The0Scorpion/2DOF_Hover/CAD/Inertias/InertiaHigherJoint.PNG

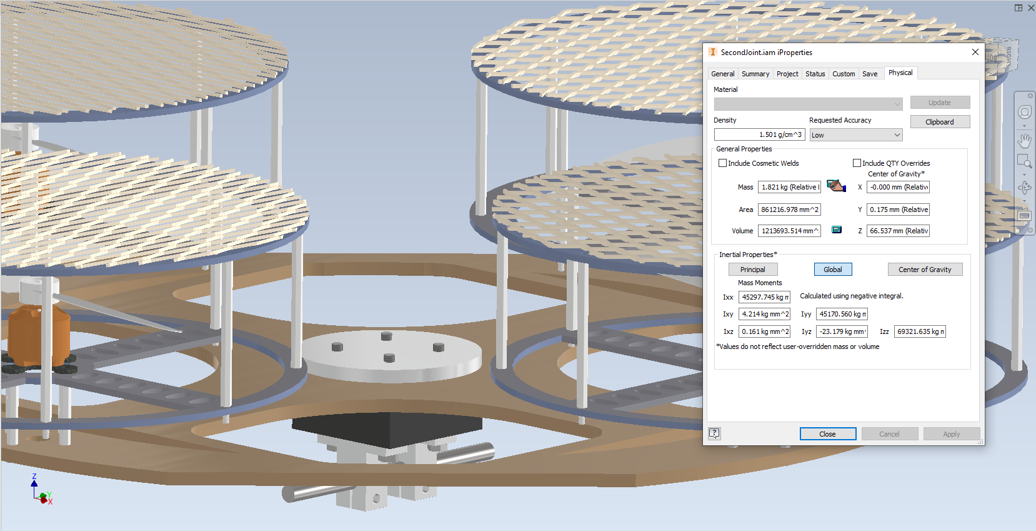
CAD/Inertias/InertiaHigherJoint.PNG
