The0Scorpion/2DOF_Hover/CAD/Inertias/LowerJoint_CG.PNG

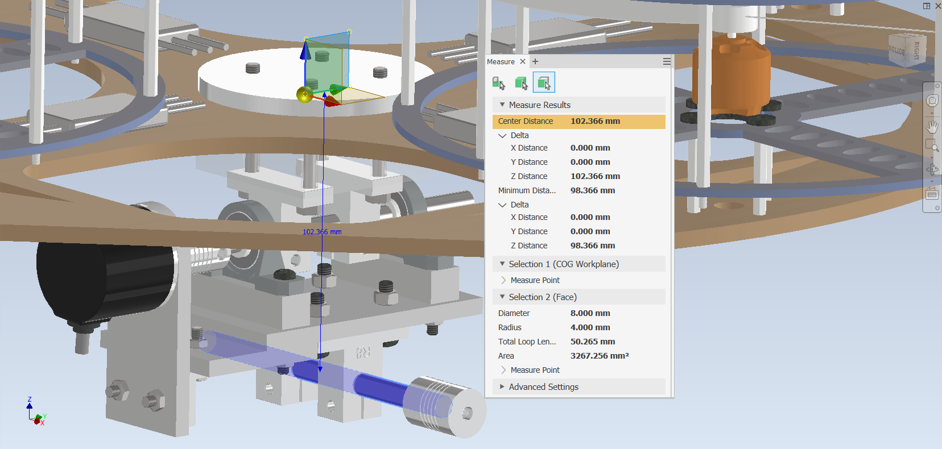
CAD/Inertias/LowerJoint_CG.PNG
