The0Scorpion/2DOF_Hover/CAD/Inertias/LowerJoint_Inertia_mass.PNG

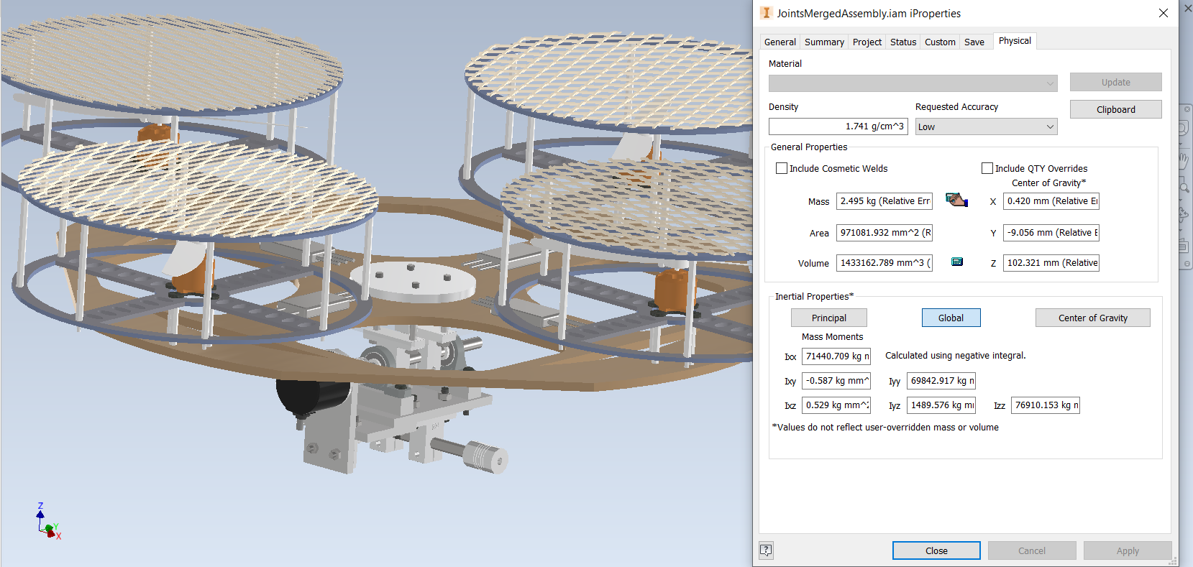
CAD/Inertias/LowerJoint_Inertia_mass.PNG
