The0Scorpion/2DOF_Hover/CAD/Inertias/LowerJoint_TorqueArm.PNG

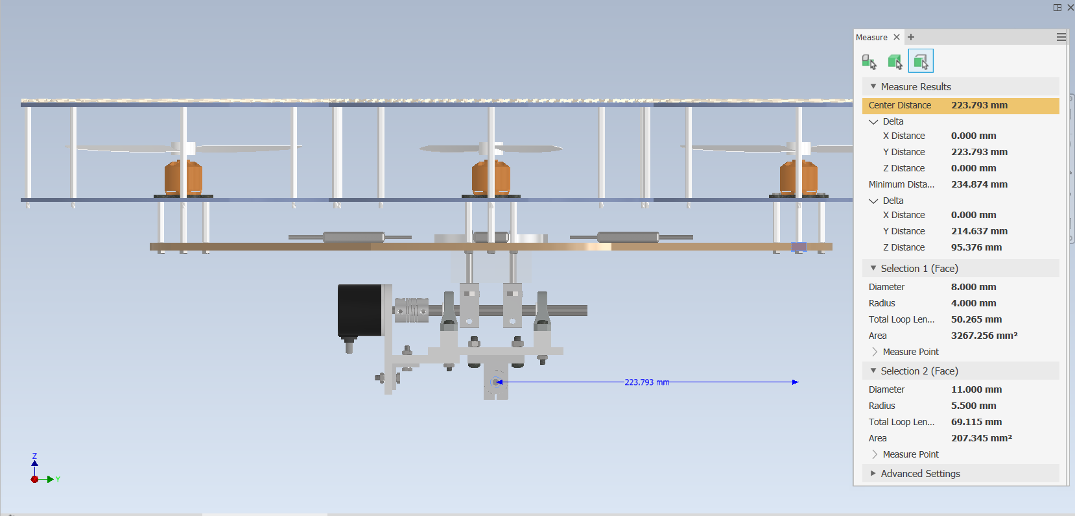
CAD/Inertias/LowerJoint_TorqueArm.PNG
