The0Scorpion/2DOF_Hover/CAD/Inertias/UpperJoint_CG.PNG

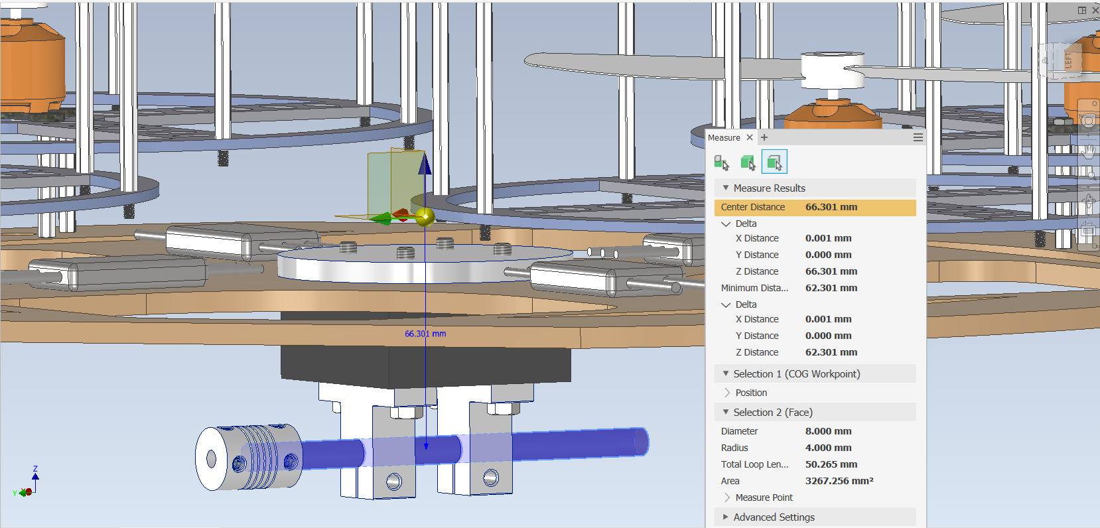
CAD/Inertias/UpperJoint_CG.PNG
