The0Scorpion/2DOF_Hover/CAD/Inertias/UpperJoint_TorqueArm.PNG

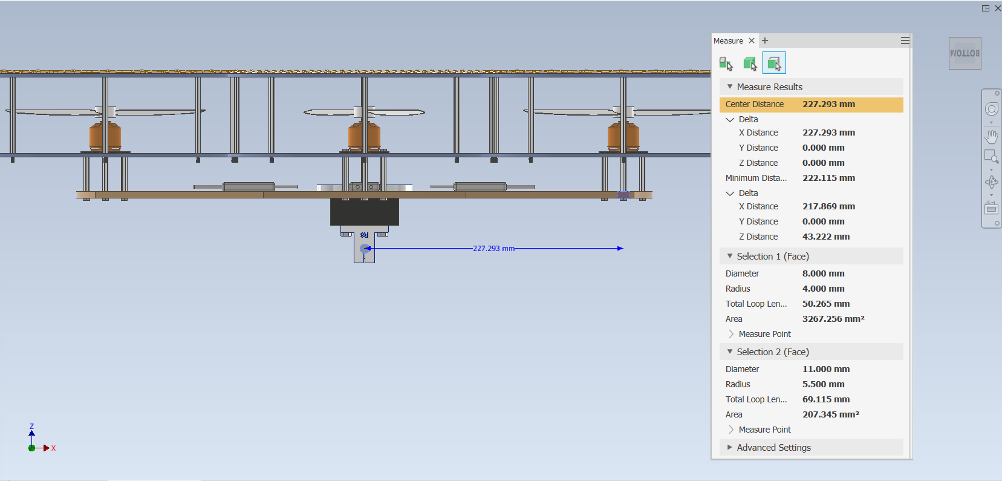
CAD/Inertias/UpperJoint_TorqueArm.PNG
