The0Scorpion/2DOF_Hover/Electric/PCB_HighQuality_2024-03-02.png

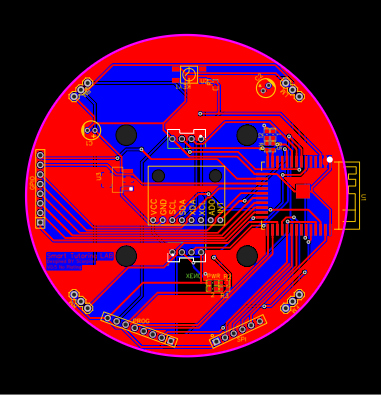
Electric/PCB_HighQuality_2024-03-02.png
