The0Scorpion/2DOF_Hover/Electric/Screenshot 2024-03-02 193824.png

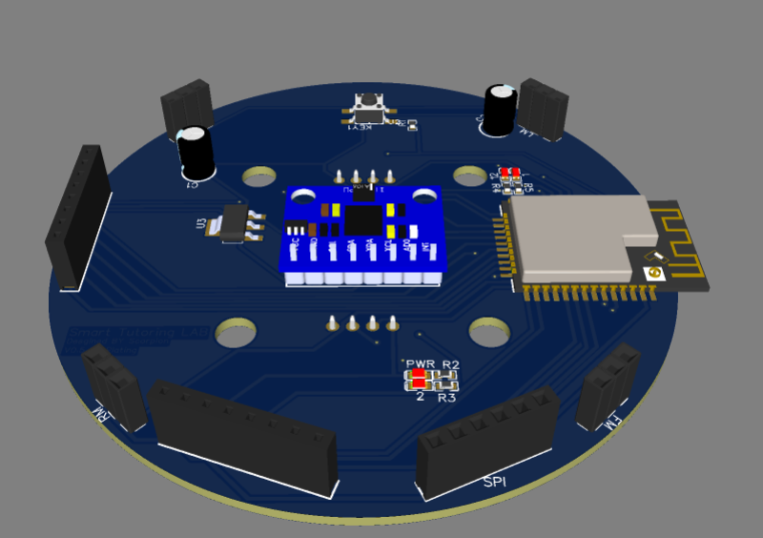
Electric/Screenshot 2024-03-02 193824.png
