The0Scorpion/2DOF_Hover/Model/MotorEstimationModel/Inertias/ArmLengthLower.PNG

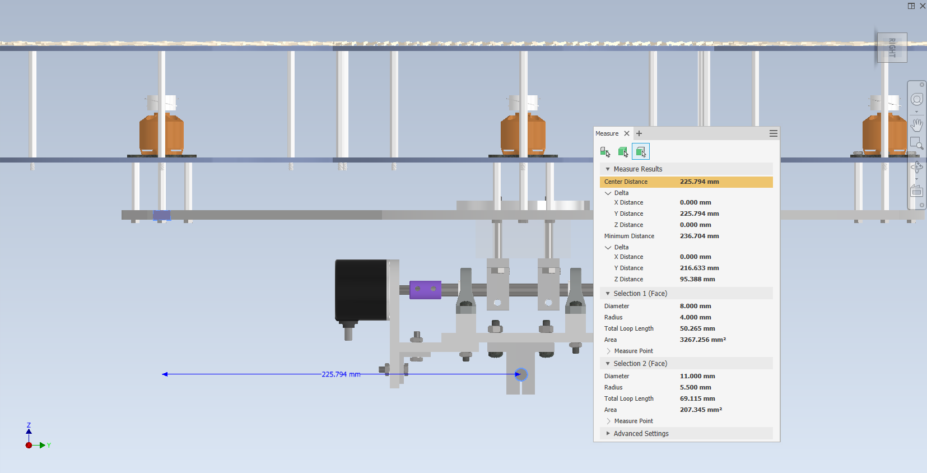
Model/MotorEstimationModel/Inertias/ArmLengthLower.PNG
