The0Scorpion/2DOF_Hover/Model/MotorEstimationModel/Inertias/ArmLengthUpper.PNG

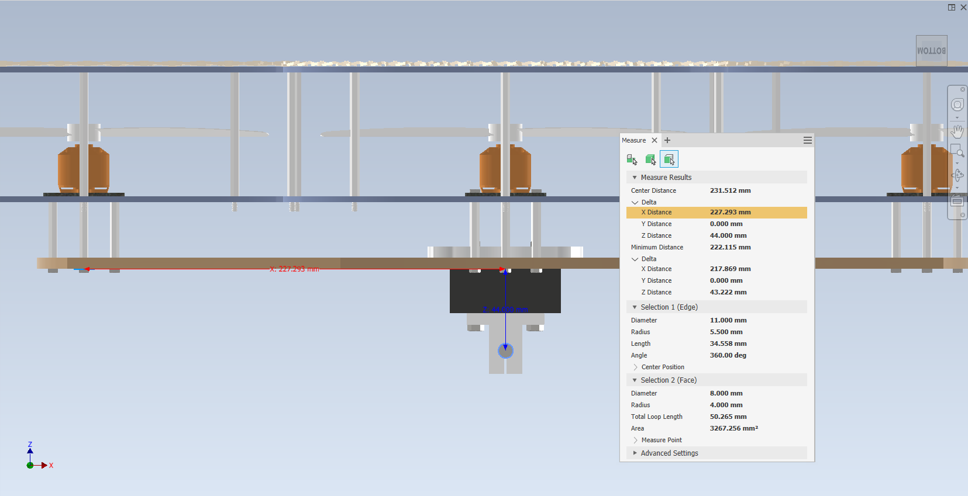
Model/MotorEstimationModel/Inertias/ArmLengthUpper.PNG
