The0Scorpion/2DOF_Hover/Model/MotorEstimationModel/Inertias/CG_LowerJoint.PNG

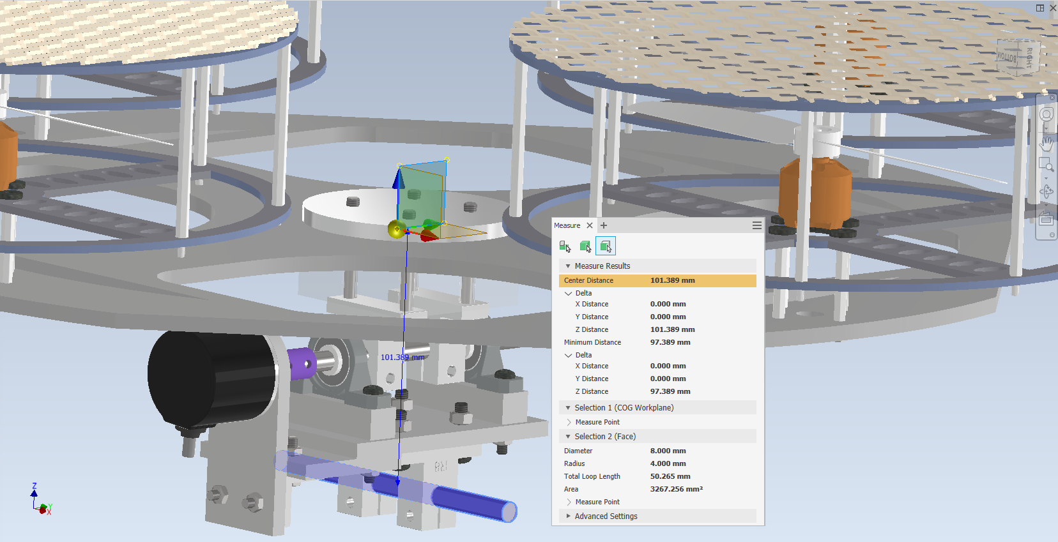
Model/MotorEstimationModel/Inertias/CG_LowerJoint.PNG
