The0Scorpion/2DOF_Hover/Model/MotorEstimationModel/Inertias/CG_UpperJoint.PNG

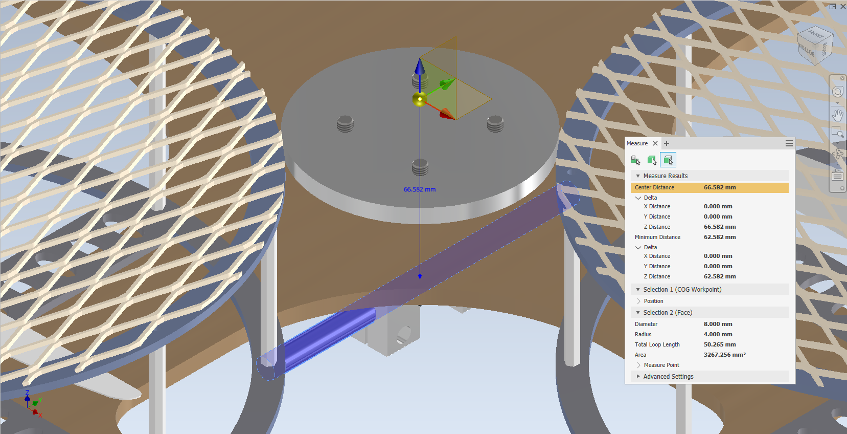
Model/MotorEstimationModel/Inertias/CG_UpperJoint.PNG
