The0Scorpion/2DOF_Hover/Model/MotorEstimationModel/Inertias/InertiaUpperJoint.PNG

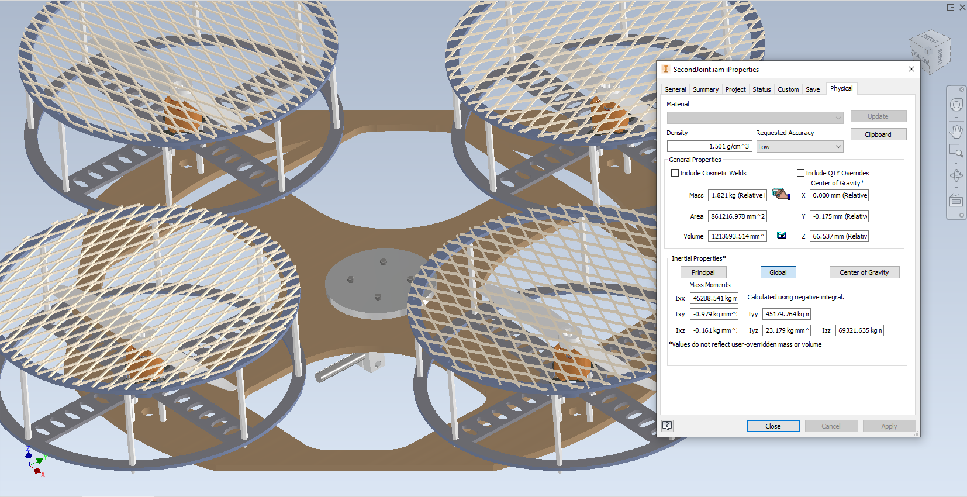
Model/MotorEstimationModel/Inertias/InertiaUpperJoint.PNG
