The0Scorpion/2DOF_Hover/Model/Roll Reduced Model/2200kv.jpg

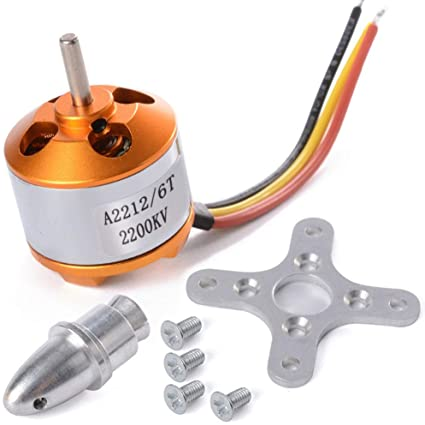
Model/Roll Reduced Model/2200kv.jpg
