The0Scorpion/2DOF_Hover/Model/Non Linear Model/2020RightAngle_ipt_a59fb1f2.STEP

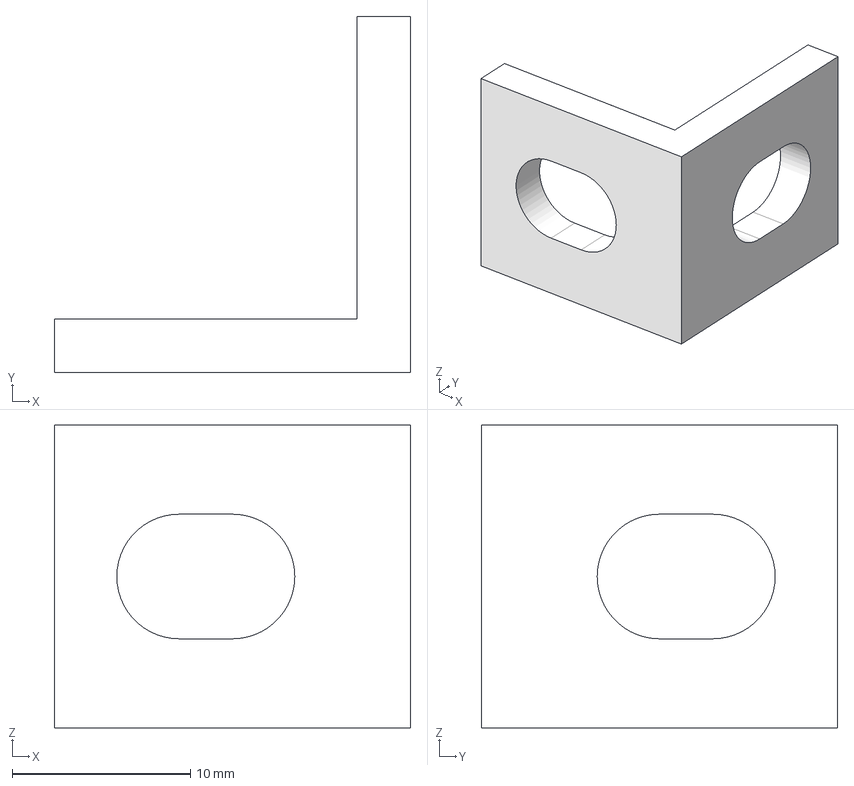
[picture p27: CAD file, 2024-03-01]
Model/Non Linear Model/2020RightAngle_ipt_a59fb1f2.STEP
20.0 x 20.0 x 17.0 mm
