The0Scorpion/2DOF_Hover/Model/Non Linear Model/BaseC_6_ipt_475c7a50.STEP

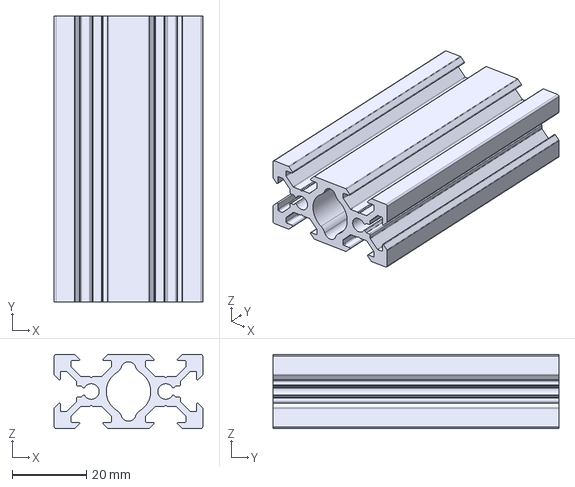
[picture p28: CAD file, 2024-03-01]
Model/Non Linear Model/BaseC_6_ipt_475c7a50.STEP
40.0 x 77.0 x 20.0 mm
