The0Scorpion/2DOF_Hover/Model/Non Linear Model/BaseC_3_ipt_c71fdd73.STEP

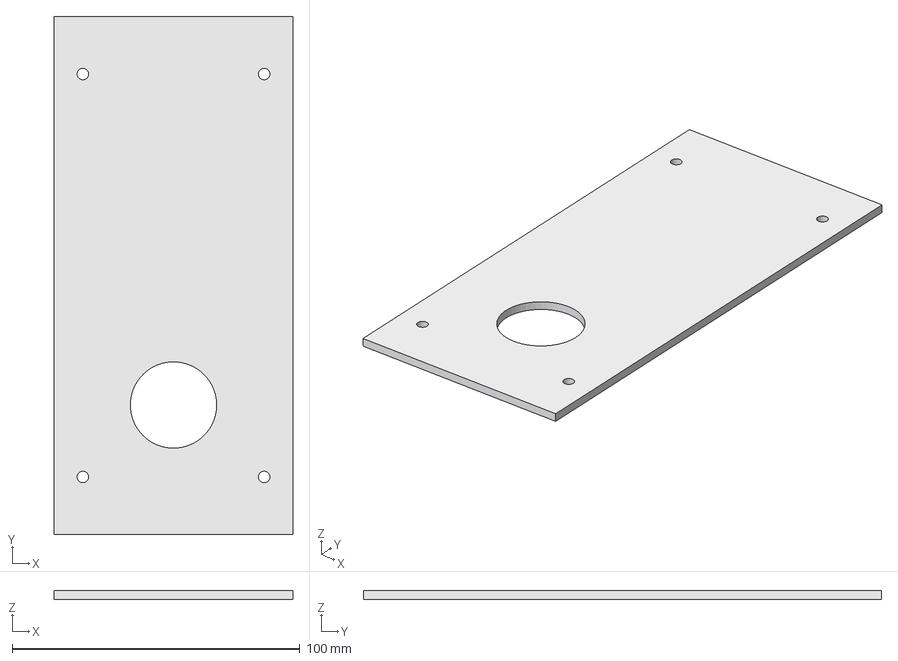
[picture p29: CAD file, 2024-03-01]
Model/Non Linear Model/BaseC_3_ipt_c71fdd73.STEP
83.0 x 180.0 x 3.00 mm
