The0Scorpion/2DOF_Hover/Model/Non Linear Model/spacers for prop_ipt_213f8d71.STEP

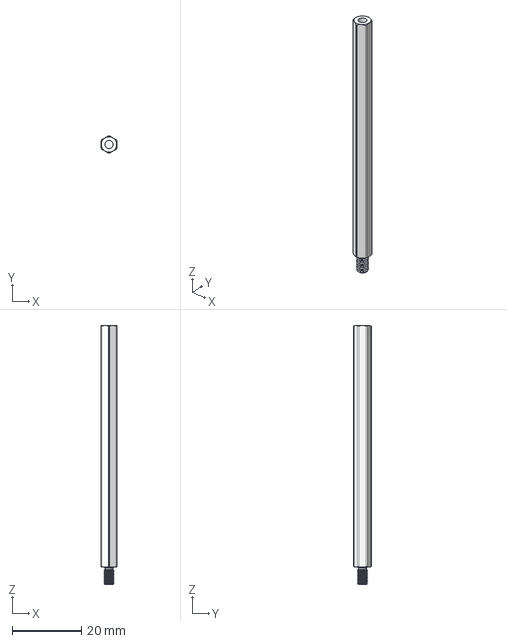
[picture p30: CAD file, 2024-03-01]
Model/Non Linear Model/spacers for prop_ipt_213f8d71.STEP
4.50 x 5.08 x 75.0 mm
