The0Scorpion/2DOF_Hover/Model/Non Linear Model/MOTOR COUPLER CONNECTOR (1)_ipt_c41452cb.STEP

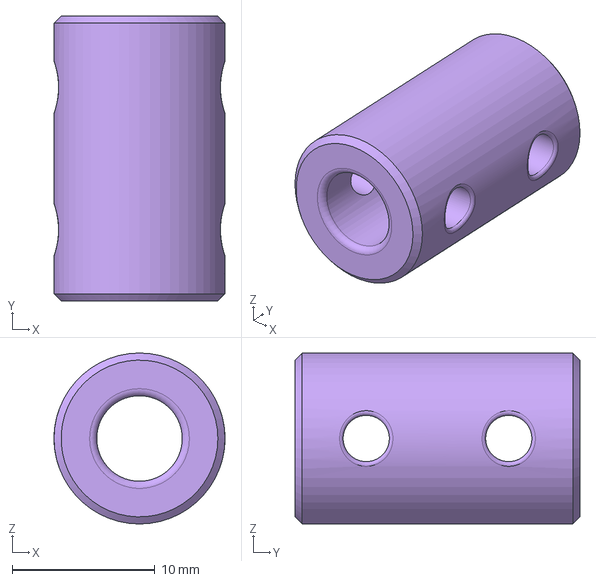
[picture p31: CAD file, 2024-03-01]
Model/Non Linear Model/MOTOR COUPLER CONNECTOR (1)_ipt_c41452cb.STEP
12.0 x 20.0 x 12.0 mm
