The0Scorpion/2DOF_Hover/Model/Non Linear Model/BaseC_4_ipt_c71fdd73.STEP

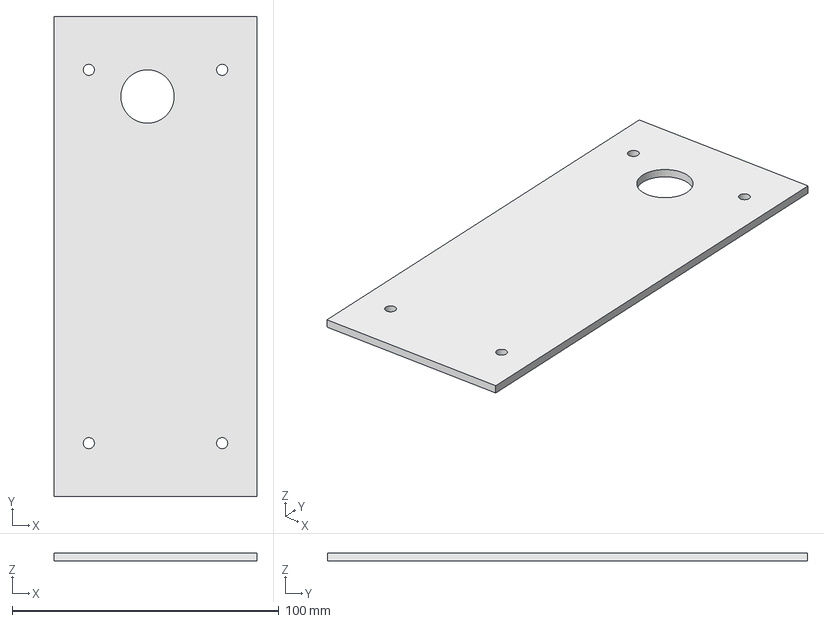
[picture p32: CAD file, 2024-03-01]
Model/Non Linear Model/BaseC_4_ipt_c71fdd73.STEP
76.0 x 180.0 x 3.00 mm
