The0Scorpion/2DOF_Hover/Model/Non Linear Model/Part1_ipt_db55b04b.STEP

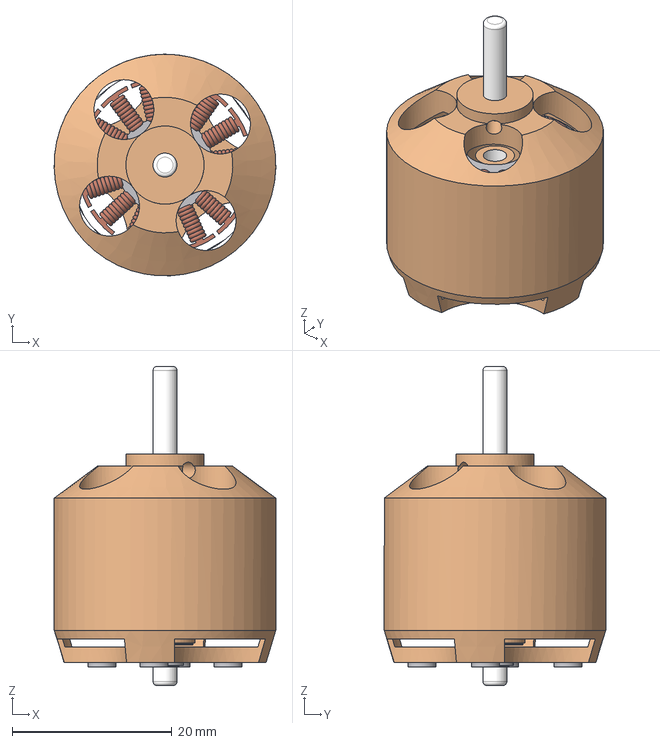
[picture p33: CAD file, 2024-03-01]
Model/Non Linear Model/Part1_ipt_db55b04b.STEP
27.8 x 27.8 x 40.0 mm
