The0Scorpion/2DOF_Hover/Model/Non Linear Model/Holder Tube-R8_ipt_e7239e0e.STEP

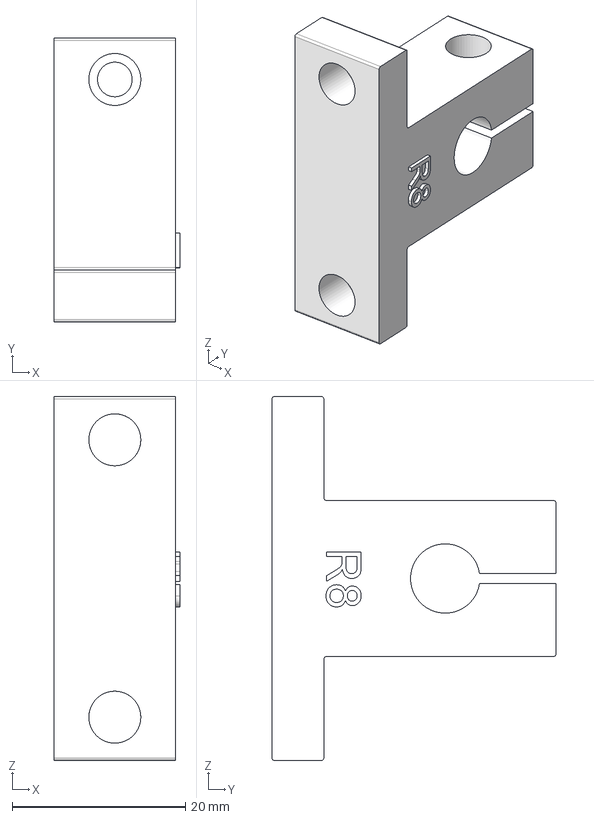
[picture p34: CAD file, 2024-03-01]
Model/Non Linear Model/Holder Tube-R8_ipt_e7239e0e.STEP
14.5 x 32.8 x 42.0 mm
