The0Scorpion/2DOF_Hover/Model/Non Linear Model/FlangedBearing8mm_ipt_45b851ef.STEP

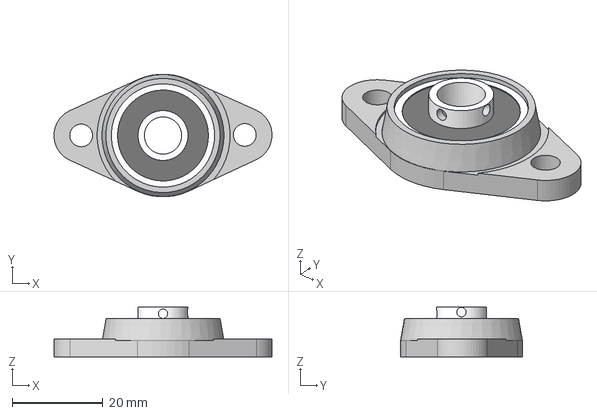
[picture p35: CAD file, 2024-03-01]
Model/Non Linear Model/FlangedBearing8mm_ipt_45b851ef.STEP
48.0 x 27.0 x 11.0 mm
