The0Scorpion/2DOF_Hover/Model/Non Linear Model/guard 2_ipt_d986c415.STEP

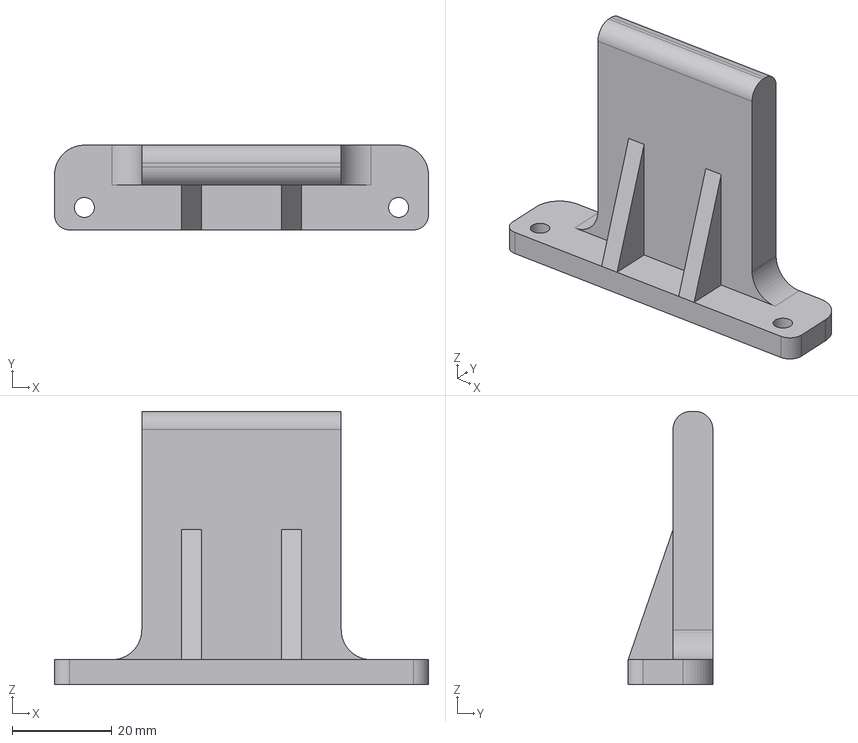
[picture p36: CAD file, 2024-03-01]
Model/Non Linear Model/guard 2_ipt_d986c415.STEP
75.0 x 17.0 x 54.8 mm
