The0Scorpion/2DOF_Hover/Model/Non Linear Model/pcb_ipt_b7a0ce45.STEP

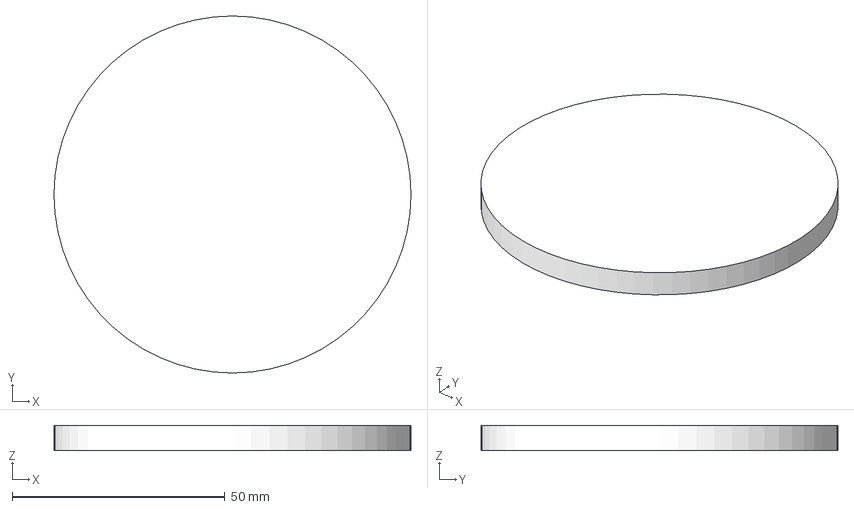
[picture p37: CAD file, 2024-03-01]
Model/Non Linear Model/pcb_ipt_b7a0ce45.STEP
84.0 x 84.0 x 6.00 mm
