The0Scorpion/2DOF_Hover/Model/Non Linear Model/gard1_ipt_e571afd1.STEP

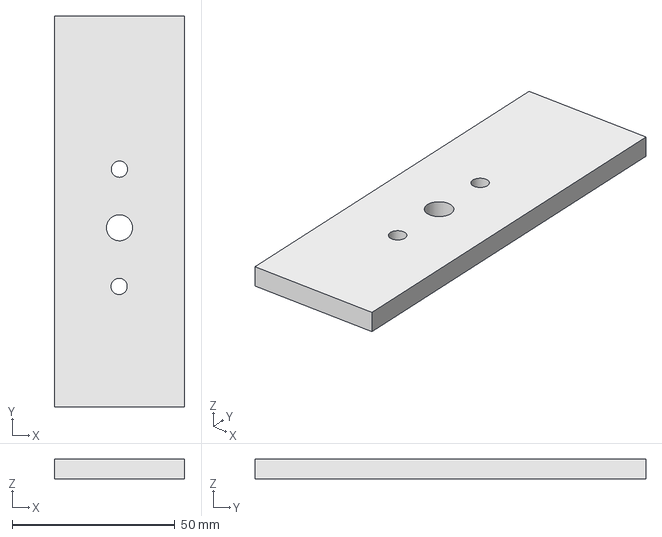
[picture p38: CAD file, 2024-03-01]
Model/Non Linear Model/gard1_ipt_e571afd1.STEP
40.0 x 120.0 x 6.00 mm
