The0Scorpion/2DOF_Hover/Model/Non Linear Model/Joint1C_1_ipt_b9e6bb9f.STEP

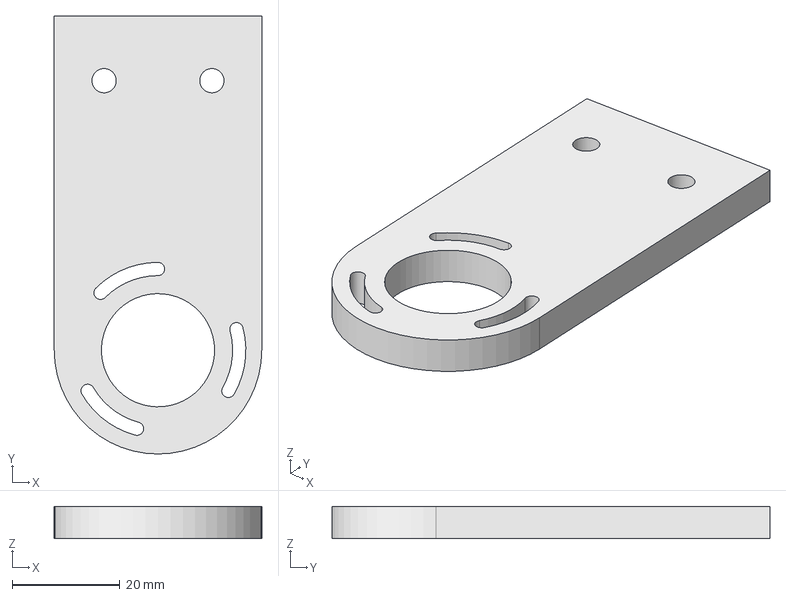
[picture p39: CAD file, 2024-03-01]
Model/Non Linear Model/Joint1C_1_ipt_b9e6bb9f.STEP
38.5 x 81.2 x 6.00 mm
