The0Scorpion/2DOF_Hover/Model/Non Linear Model/interplate_ipt_43879ff1.STEP

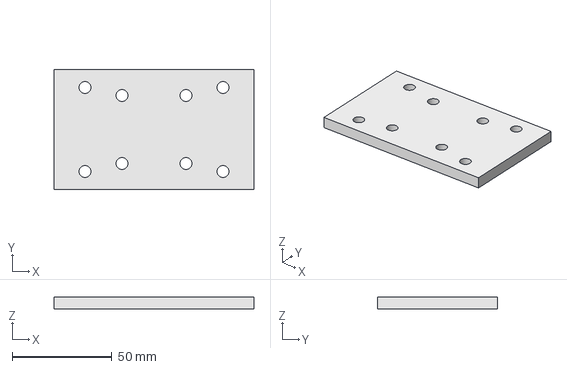
[picture p40: CAD file, 2024-03-01]
Model/Non Linear Model/interplate_ipt_43879ff1.STEP
100.0 x 60.0 x 6.00 mm
