The0Scorpion/2DOF_Hover/Model/Non Linear Model/Part18_ipt_c51c05df.STEP

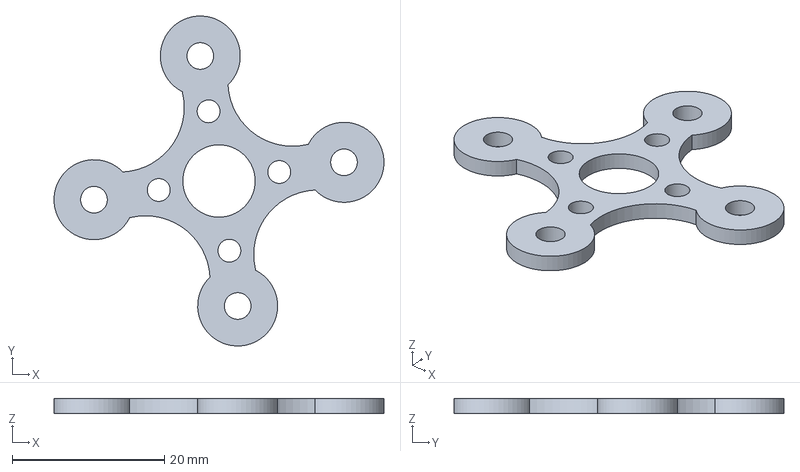
[picture p41: CAD file, 2024-03-01]
Model/Non Linear Model/Part18_ipt_c51c05df.STEP
43.3 x 43.3 x 2.00 mm
