The0Scorpion/2DOF_Hover/Model/Non Linear Model/Standoff M3 M-M H 45mm_ipt_213f8d71.STEP

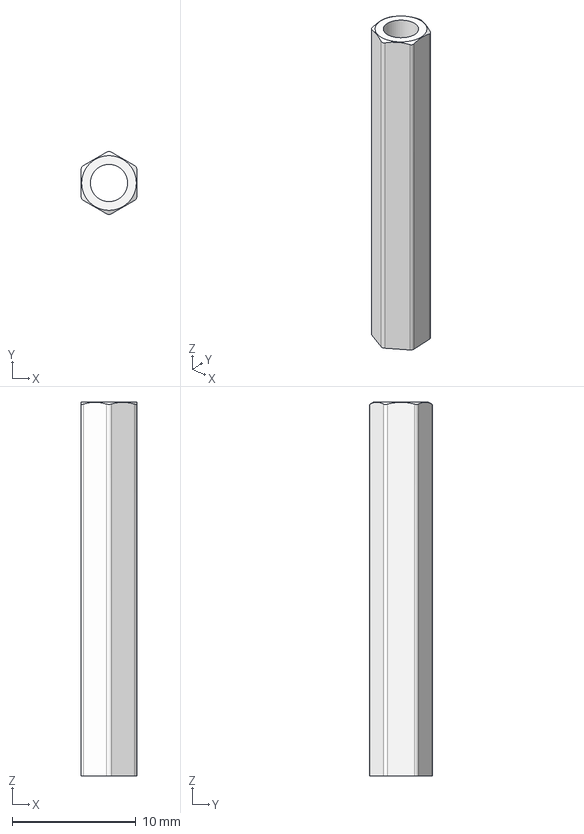
[picture p42: CAD file, 2024-03-01]
Model/Non Linear Model/Standoff M3 M-M H 45mm_ipt_213f8d71.STEP
4.50 x 5.08 x 30.2 mm
