The0Scorpion/2DOF_Hover/Model/Non Linear Model/Part15_ipt_e31f6ad0.STEP

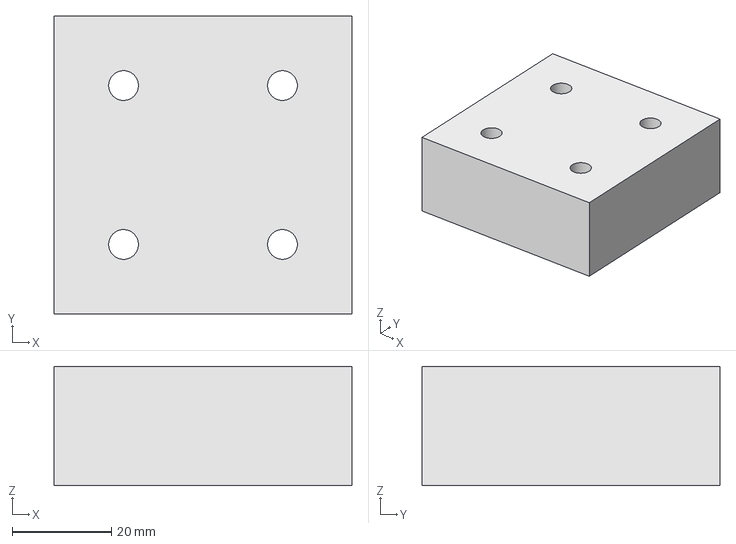
[picture p43: CAD file, 2024-03-01]
Model/Non Linear Model/Part15_ipt_e31f6ad0.STEP
60.0 x 60.0 x 24.0 mm
