The0Scorpion/2DOF_Hover/Model/Non Linear Model/Part17_ipt_34ea8653.STEP

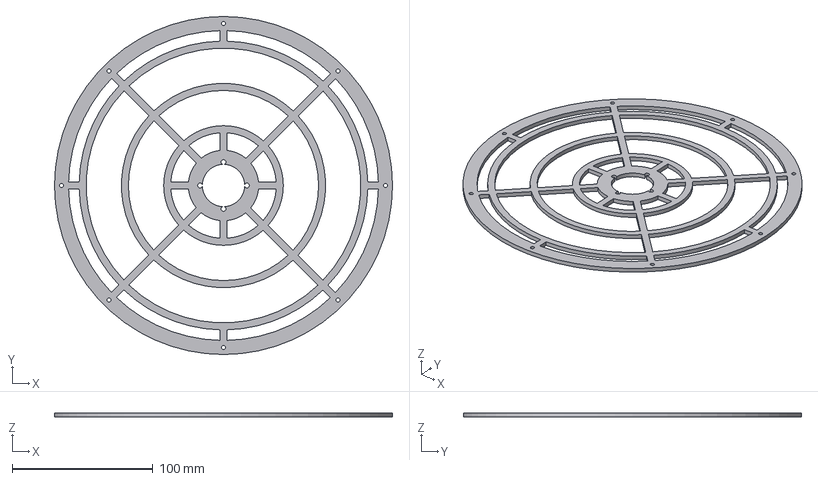
[picture p44: CAD file, 2024-03-01]
Model/Non Linear Model/Part17_ipt_34ea8653.STEP
240.0 x 240.0 x 3.00 mm
