The0Scorpion/2DOF_Hover/Model/Non Linear Model/plummer blockPowe_ipt_5ba01ddb.STEP

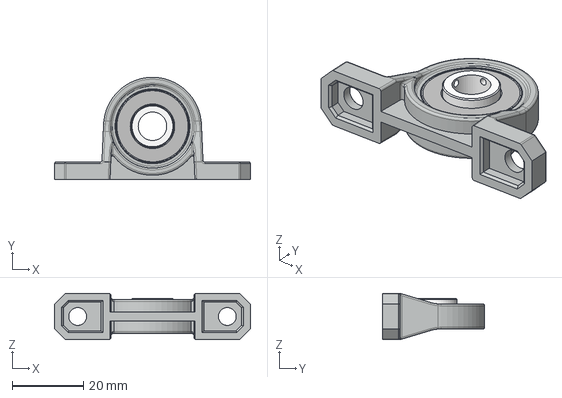
[picture p45: CAD file, 2024-03-01]
Model/Non Linear Model/plummer blockPowe_ipt_5ba01ddb.STEP
55.0 x 28.8 x 13.0 mm
