The0Scorpion/2DOF_Hover/Model/Non Linear Model/9. Fan_ipt_4f385e48.STEP

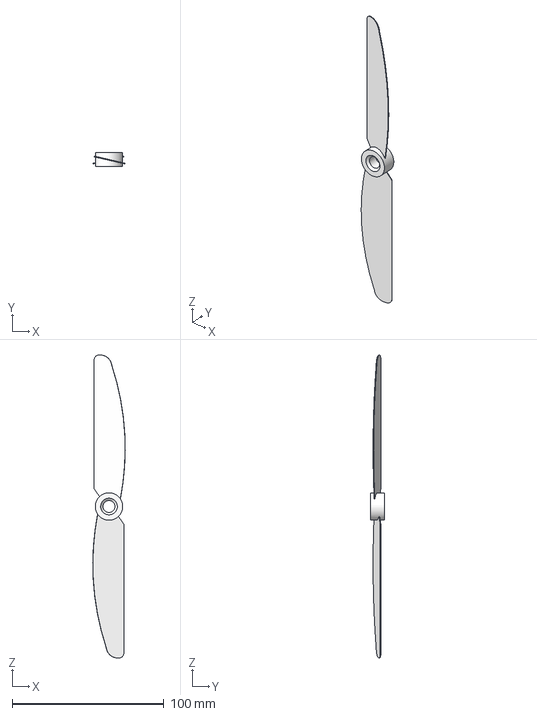
[picture p46: CAD file, 2024-03-01]
Model/Non Linear Model/9. Fan_ipt_4f385e48.STEP
21.4 x 9.42 x 199.4 mm
