The0Scorpion/2DOF_Hover/Model/Non Linear Model/BaseC_7_ipt_b9e6bb9f.STEP

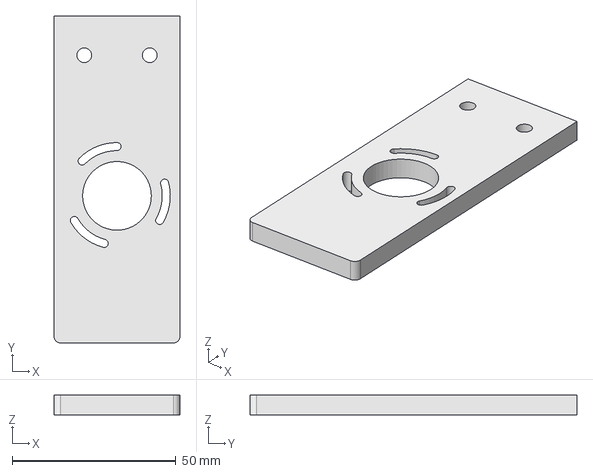
[picture p47: CAD file, 2024-03-01]
Model/Non Linear Model/BaseC_7_ipt_b9e6bb9f.STEP
38.5 x 100.0 x 6.00 mm
