The0Scorpion/2DOF_Hover/Model/Non Linear Model/BaseC_1_ipt_dbc63049.STEP

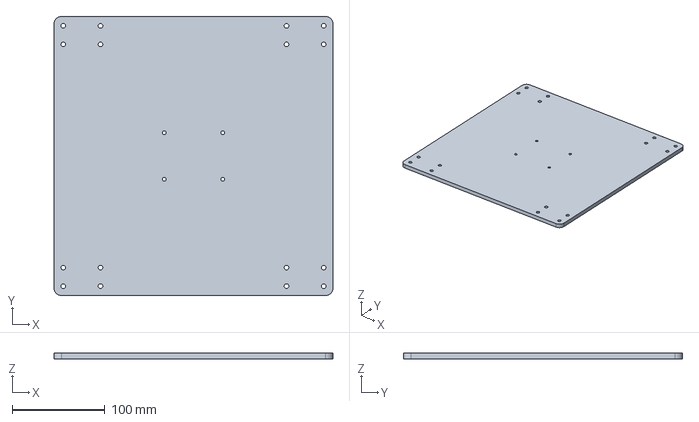
[picture p48: CAD file, 2024-03-01]
Model/Non Linear Model/BaseC_1_ipt_dbc63049.STEP
300.0 x 300.0 x 6.00 mm
