The0Scorpion/2DOF_Hover/Model/Non Linear Model/plateplummer_ipt_bf847d22.STEP

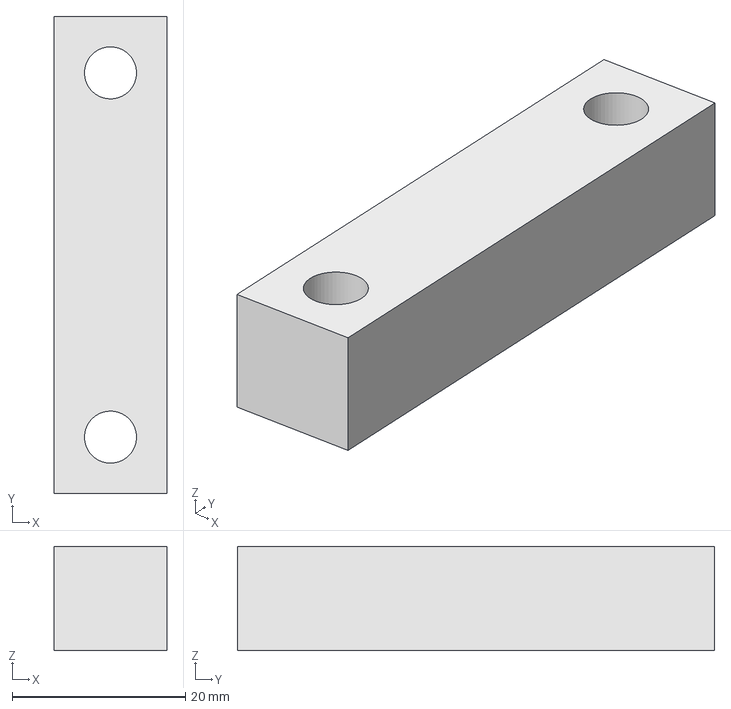
[picture p49: CAD file, 2024-03-01]
Model/Non Linear Model/plateplummer_ipt_bf847d22.STEP
13.0 x 55.0 x 12.0 mm
