The0Scorpion/2DOF_Hover/Model/Non Linear Model/BaseC_9_ipt_bd9223d9.STEP

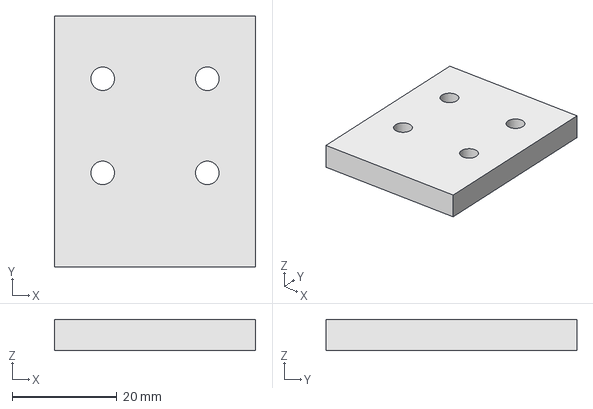
[picture p50: CAD file, 2024-03-01]
Model/Non Linear Model/BaseC_9_ipt_bd9223d9.STEP
38.5 x 48.0 x 6.00 mm
