The0Scorpion/2DOF_Hover/Model/Non Linear Model/20x20mm V-Slot_ipt_b09f816c.STEP

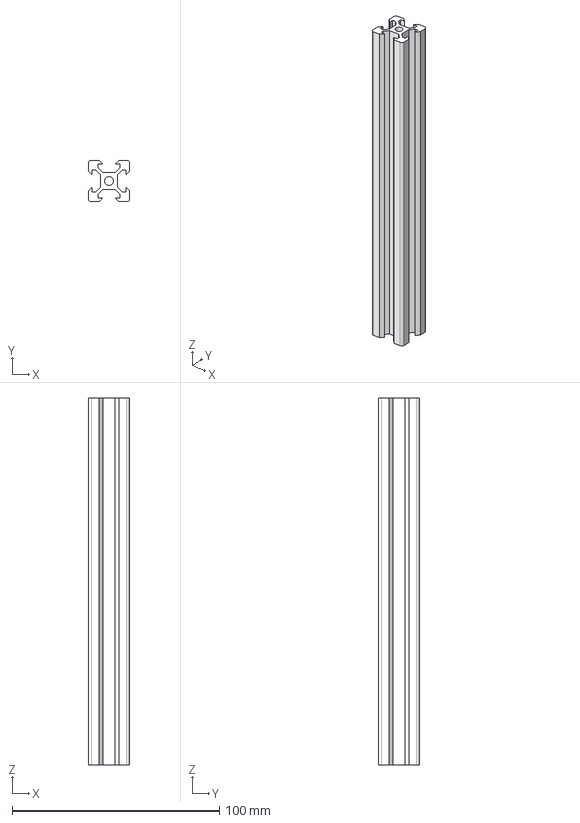
[picture p51: CAD file, 2024-03-01]
Model/Non Linear Model/20x20mm V-Slot_ipt_b09f816c.STEP
20.0 x 20.0 x 177.0 mm
