The0Scorpion/2DOF_Hover/Model/Non Linear Model/plateencoder_ipt_139437e7.STEP

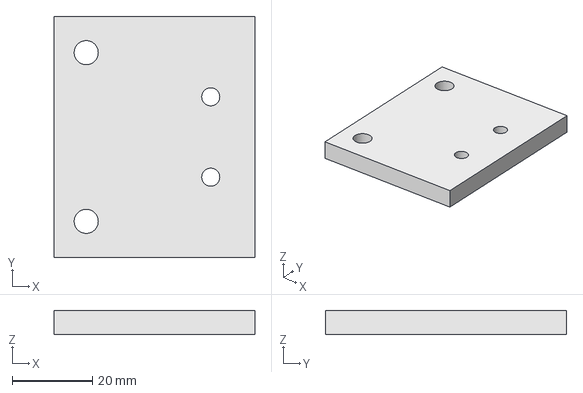
[picture p52: CAD file, 2024-03-01]
Model/Non Linear Model/plateencoder_ipt_139437e7.STEP
50.0 x 60.0 x 6.00 mm
