The0Scorpion/2DOF_Hover/Model/Non Linear Model/guard3_ipt_8caca9e3.STEP

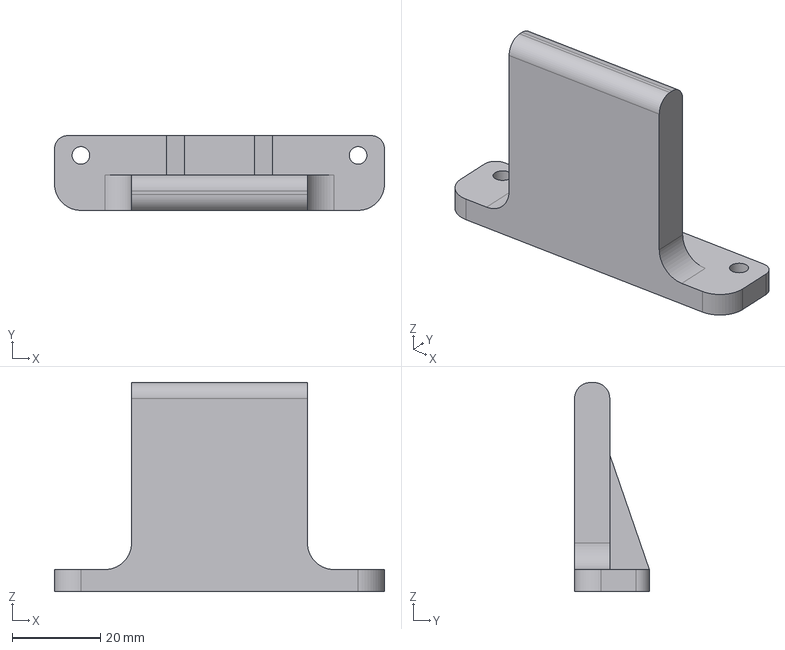
[picture p53: CAD file, 2024-03-01]
Model/Non Linear Model/guard3_ipt_8caca9e3.STEP
75.0 x 17.0 x 47.5 mm
