The0Scorpion/2DOF_Hover/Model/Non Linear Model/Part16_ipt_fb07ed32.STEP

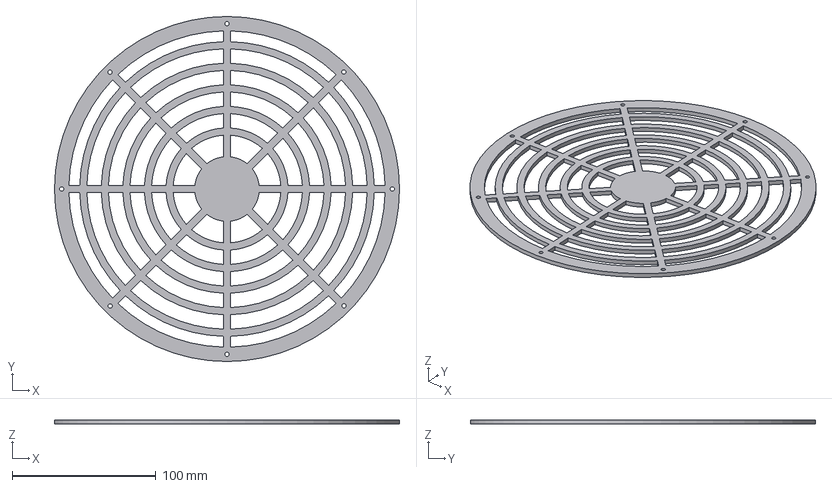
[picture p54: CAD file, 2024-03-01]
Model/Non Linear Model/Part16_ipt_fb07ed32.STEP
240.0 x 240.0 x 3.00 mm
