The0Scorpion/2DOF_Hover/Model/Non Linear Model/BaseC_5_ipt_c71fdd73.STEP

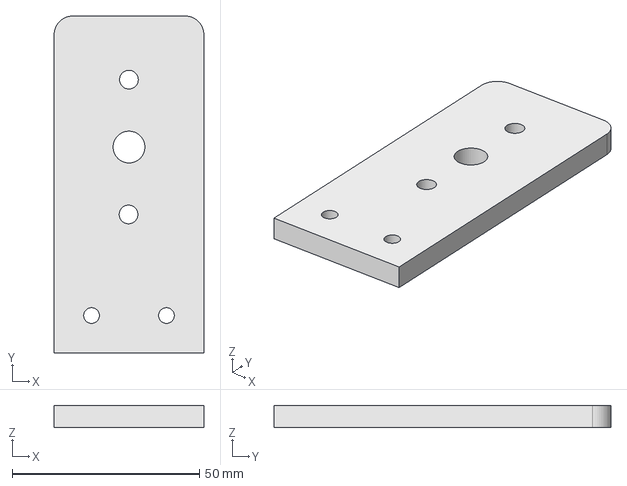
[picture p55: CAD file, 2024-03-01]
Model/Non Linear Model/BaseC_5_ipt_c71fdd73.STEP
40.0 x 90.0 x 6.00 mm
