The0Scorpion/2DOF_Hover/Data/MQTT_Delay_Test2024-03-17 18-24.xlsx

Pkt ID | pkt Size | Send Time | Receive Time | pkt Delay(ms) | Time from last pkt
1 | 121 | 1710692800280 | 1710692800314 | 34 | 500
2 | 121 | 1710692800780 | 1710692800818 | 38 | 504
3 | 121 | 1710692801280 | 1710692801315 | 35 | 497
4 | 121 | 1710692801780 | 1710692801827 | 47 | 512
5 | 121 | 1710692802280 | 1710692802318 | 38 | 491 | Test Conditions:
6 | 121 | 1710692802780 | 1710692802840 | 60 | 522 | NTP Server: | time.aws.com
7 | 121 | 1710692803280 | 1710692803315 | 35 | 475 | pkt Size | 121
8 | 121 | 1710692803780 | 1710692803815 | 35 | 500 | RTT to AWS | 44ms | (measured on same network)
9 | 121 | 1710692804280 | 1710692804316 | 36 | 501 | RTT to AWS NTP | 280ms | (measured on same network)
10 | 122 | 1710692804780 | 1710692804814 | 34 | 498 | RTT to google dns | 44ms | (measured on same network)
11 | 122 | 1710692805280 | 1710692805325 | 45 | 511
12 | 122 | 1710692805780 | 1710692805822 | 42 | 497
13 | 122 | 1710692806280 | 1710692806319 | 39 | 497
14 | 122 | 1710692806780 | 1710692806816 | 36 | 497
15 | 122 | 1710692807280 | 1710692807317 | 37 | 501
16 | 122 | 1710692807780 | 1710692807816 | 36 | 499
17 | 122 | 1710692808280 | 1710692808314 | 34 | 498
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
