The0Scorpion/2DOF_Hover/Data/MQTT_Delay_Test2024-03-17 19-03.xlsx

Pkt ID | pkt Size | Send Time | Receive Time | pkt Delay(ms) (ESP TIME TO AWS) | Time from last pkt(Esp Time) | Local Time | LocalEpoch | Delay(Local Time to NodeJS Client) | Time from last pkt (in local Time)
1 | 121 | 1710695014510 | 1710695014539 | 29 | 500 | 19:03:34.514 | 68614514 | 25.00 | 500
2 | 121 | 1710695015010 | 1710695015042 | 32 | 503 | 19:03:34.985 | 68614985 | 57.00 | 471
3 | 121 | 1710695015510 | 1710695015541 | 31 | 499 | 19:03:35.502 | 68615502 | 39.00 | 517 | Test Conditions:
4 | 121 | 1710695016010 | 1710695016041 | 31 | 500 | 19:03:35.973 | 68615973 | 68.00 | 471 | NTP Server: | time.aws.com
5 | 121 | 1710695016510 | 1710695016539 | 29 | 498 | 19:03:36.490 | 68616490 | 49.00 | 517 | pkt Size | 121
6 | 121 | 1710695017010 | 1710695017039 | 29 | 500 | 19:03:37.011 | 68617011 | 28.00 | 521 | RTT to AWS | 44ms | (measured on same network)
7 | 121 | 1710695017510 | 1710695017539 | 29 | 500 | 19:03:37.480 | 68617480 | 59.00 | 469 | RTT to AWS NTP | 180ms | (measured on same network) | SpeedTest:
8 | 121 | 1710695018010 | 1710695018053 | 43 | 514 | 19:03:37.998 | 68617998 | 55.00 | 518 | RTT to google dns | 44ms | (measured on same network) | Down: | 31Mbps | 108ms
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
