The0Scorpion/2DOF_Hover/Codes/PID_test/Test1.PNG

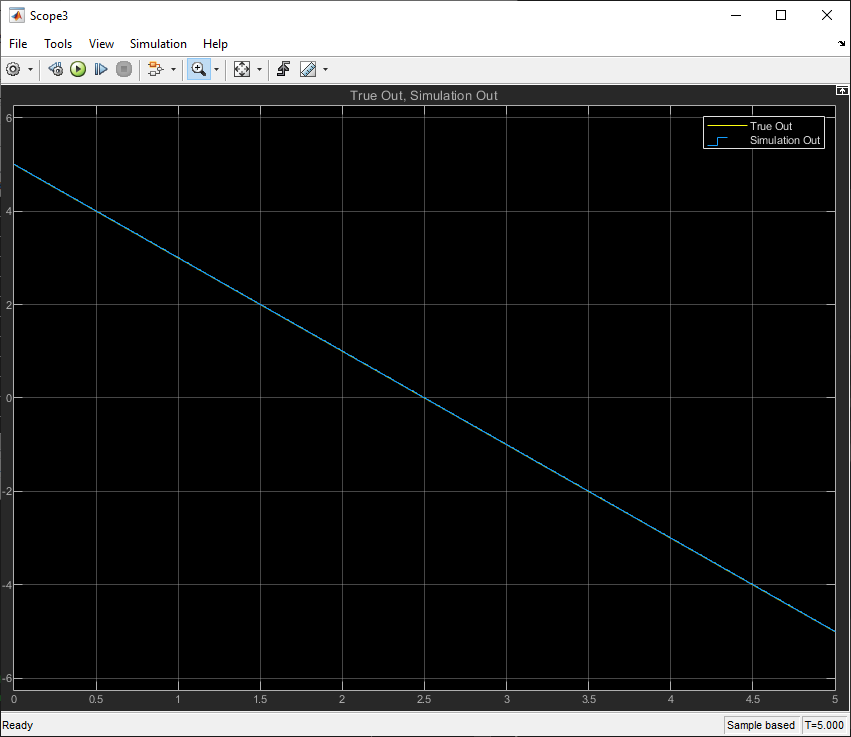
Codes/PID_test/Test1.PNG
