The0Scorpion/2DOF_Hover/Codes/PID_test/Test2.PNG

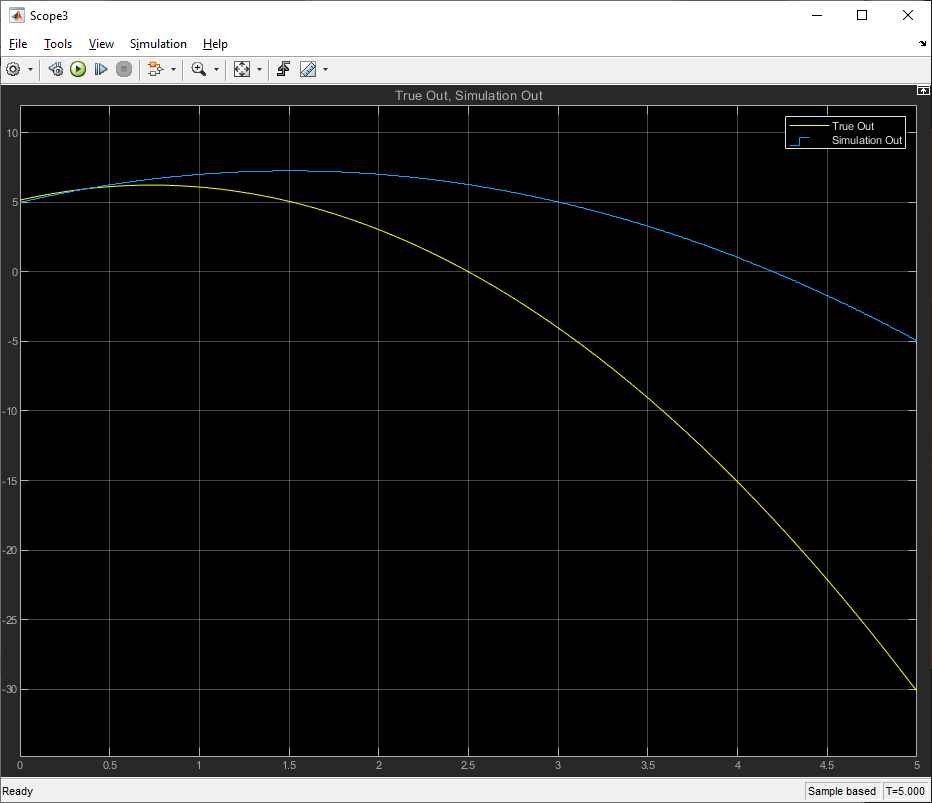
Codes/PID_test/Test2.PNG
