The0Scorpion/2DOF_Hover/Codes/PID_test/Test3.PNG

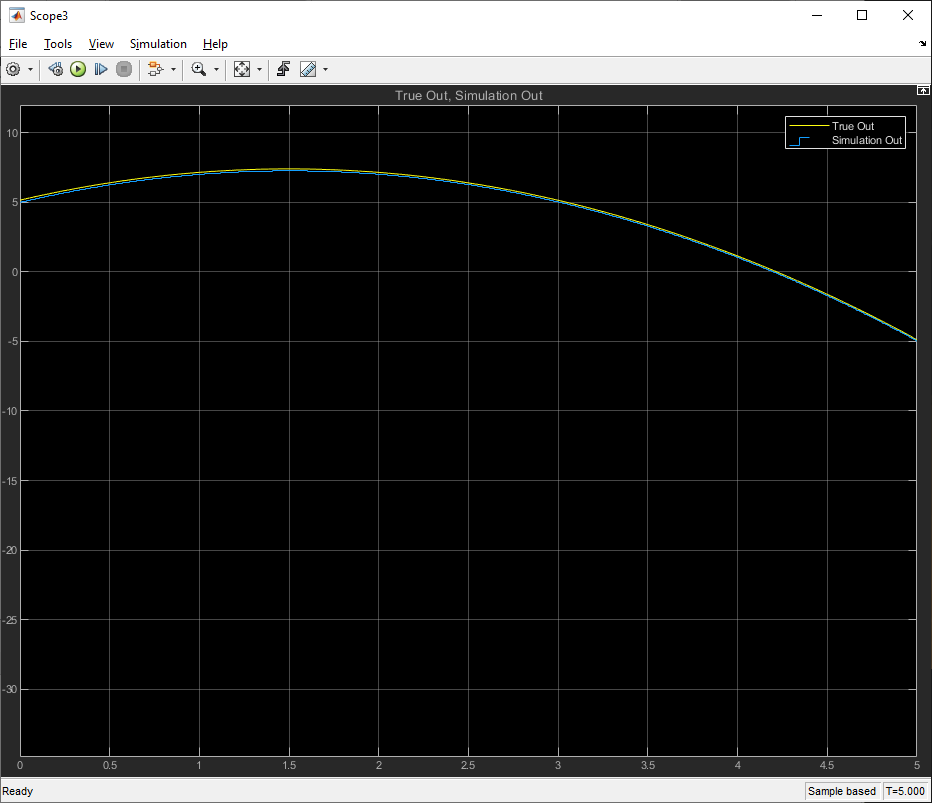
Codes/PID_test/Test3.PNG
