The0Scorpion/2DOF_Hover/Codes/2DOF_Full_Code/commonFunctions.h

/*
   Header file with the main loop and common functions
   Credit:Scorpion
   Created: 20/10/2023
*/

// #define DebugCF
#define DebugCF1

void PIDLoop(void *parameter)
{

  /*
    Main Control Loop, Runs each sampling time
  */
  initEncoder(0, 0);

  if (load)
  { // get Last saved Paramters
    int pos = 2;
    xposkp = EEPROM.read(pos);
    pos += 4;
    xposki = EEPROM.read(pos);
    pos += 4;
    xposkd = EEPROM.read(pos);
    pos += 4;

    xvelkp = EEPROM.read(pos);
    pos += 4;
    xvelki = EEPROM.read(pos);
    pos += 4;
    xvelkd = EEPROM.read(pos);
    pos += 4;

    yposkp = EEPROM.read(pos);
    pos += 4;
    yposki = EEPROM.read(pos);
    pos += 4;
    yposkd = EEPROM.read(pos);
    pos += 4;

    yvelkp = EEPROM.read(pos);
    pos += 4;
    yvelki = EEPROM.read(pos);
    pos += 4;
    yvelkd = EEPROM.read(pos);
  }
  else if (save)
  { // save initial paramters
    int pos = 2;
    EEPROM.write(pos, xposkp);
    pos += 4;
    EEPROM.write(pos, xposki);
    pos += 4;
    EEPROM.write(pos, xposkd);
    pos += 4;

    EEPROM.write(pos, xvelkp);
    pos += 4;
    EEPROM.write(pos, xvelki);
    pos += 4;
    EEPROM.write(pos, xvelkd);
    pos += 4;

    EEPROM.write(pos, yposkp);
    pos += 4;
    EEPROM.write(pos, yposki);
    pos += 4;
    EEPROM.write(pos, yposkd);
    pos += 4;

    EEPROM.write(pos, yvelkp);
    pos += 4;
    EEPROM.write(pos, yvelki);
    pos += 4;
    EEPROM.write(pos, yvelkd);

    EEPROM.commit();
  }

#ifdef OFFLINE
  Work = EEPROM.read(0) > 1 ? 0 : !EEPROM.read(0);
  EEPROM.write(0, Work); // toggles running on resets
  EEPROM.commit();
#endif

  while (1)
  {
    if (Work)
    {
      initESCs(FrontMotorPIN, RightMotorPIN, BackMotorPIN, LeftMotorPIN);
      delay(2500); // wait for esc calib
#ifdef DebugCF
      Serial.println("init PID Loops");
      Serial.println("With Paramters:");
      Serial.print("xposkp: ");
      Serial.println(xposkp);
      Serial.print("xposki: ");
      Serial.println(xposki);
      Serial.print("xposkd: ");
      Serial.println(xposkd);
      Serial.print("xposSet: ");
      Serial.println(xposSet);

      Serial.print("xvelkp: ");
      Serial.println(xvelkp);
      Serial.print("xvelki: ");
      Serial.println(xvelki);
      Serial.print("xvelkd: ");
      Serial.println(xvelkd);

      Serial.print("yposkp: ");
      Serial.println(yposkp);
      Serial.print("yposki: ");
      Serial.println(yposki);
      Serial.print("yposkd: ");
      Serial.println(yposkd);
      Serial.print("yposSet: ");
      Serial.println(yposSet);

      Serial.print("yvelkp: ");
      Serial.println(yvelkp);
      Serial.print("yvelki: ");
      Serial.println(yvelki);
      Serial.print("yvelkd: ");
      Serial.println(yvelkd);
#endif

      // Startup
#ifdef DebugCF
      Serial.println("Start Up");
#endif
      StartUP(0.20, 0.20);
#ifdef DebugCF
      Serial.println("Started");
#endif
// Reset and Create 4 PID objects with specified parameters
    resetPID(&xPOSPID);
    initializePID(&xPOSPID, xposkp, xposki, xposkd, xposSet, -PositionLoopSat, PositionLoopSat); // to be rechecked the limits
    resetPID(&xVELPID);
    initializePID(&xVELPID, xvelkp, xvelki, xvelkd, xvelSet, -xmaxDeltaMicros / 10, xmaxDeltaMicros / 10);
    resetPID(&yPOSPID);
    initializePID(&yPOSPID, yposkp, yposki, yposkd, yposSet, -PositionLoopSat, PositionLoopSat); // to be rechecked the limits
    resetPID(&yVELPID);
    initializePID(&yVELPID, yvelkp, yvelki, yvelkd, yvelSet, -ymaxDeltaMicros / 10, ymaxDeltaMicros / 10);

    XRVG0_U.Y1target = xposSet;
    YRVG0_U.Y1target = yposSet;

#ifdef DebugCF
    Serial.println("init PID Loops Success");
#endif

    // PIDLastTime1 = micros();
    TickType_t PIDLastTime1;
    const TickType_t xFrequency = 5 / portTICK_PERIOD_MS;

    // Initialise the xLastWakeTime variable with the current time.
    PIDLastTime1 = xTaskGetTickCount();
#ifdef DebugCF // just for debugging
    Serial.println("PID Started");
#endif

    while (PID_Running && Work)
    {
      SendToMQTT = 1;
      // Update feedback values using sensor fusion
      xSpeed = getxSpeed();
      ySpeed = getySpeed();

      // updateIMU();
      // xSpeed = (1 - IMU_FusionPrio) * xSpeed + IMU_FusionPrio * AngleToCounts(xDotIMU);
      // ySpeed = (1 - IMU_FusionPrio) * ySpeed + IMU_FusionPrio * AngleToCounts(yDotIMU);

      // calcualte RVG
      RVG0_step();
      xPOSPID.setpoint = XRVG0_Y.Y1ref;
      yPOSPID.setpoint = XRVG0_Y.Y1ref;

      // Calculate velocity SP from positionPID output
      xVELPID.setpoint = (float)calculatePID(&xPOSPID, CountsToAngle(xEncoderCount)) + XRVG0_Y.Y2ref;
      yVELPID.setpoint = (float)calculatePID(&yPOSPID, CountsToAngle(yEncoderCount)) + YRVG0_Y.Y2ref;

      // Calculate action for motors from velocityPID output
      xAction = (float)calculatePID(&xVELPID, xSpeed) * 10; // convert from Percnt to micros (Pulse width)
      yAction = (float)calculatePID(&yVELPID, ySpeed) * 10; // convert from Percnt to micros (Pulse width)
      writeControlAction((int)xAction, (int)yAction);

      counta++;
      if (counta > RunSamples)
      {
        counta = 0;
        Work = 0;
        PID_Running = 0;
        failed_Trials = 0;
        DisableMotors();
        break;
      }
      vTaskDelayUntil(&PIDLastTime1, xFrequency);

      if (abs(CountsToAngle(xEncoderCount)) > xposSetLimit || abs(CountsToAngle(yEncoderCount)) > yposSetLimit)
      {
        if (failcount == 0)
        {
          failcount = counta;
        }
        else
        {
          if (counta - failcount > failLimit)
          {
            PID_Running = 0;
            failed_Trials++;
            if (failed_Trials > fail_TrailLimit)
            {
              PID_Running = 0;
              Work = 0;
              failed_Trials = 0;
              break;
              // Startup
#ifdef DebugCF
              Serial.println("Start Up");
#endif
              StartUP(0.20, 0.20);
#ifdef DebugCF
              Serial.println("Started");
#endif
            }
          }
        }
      }
      else
      {
        failcount = 0;
      }
#ifdef debugTime
      Serial.print(micros() - PIDLastTime1);
#endif

#ifdef DebugCF1 // just for debugging
      Serial.print("Counter For PID: ");
      Serial.println(counta);
#endif
    }
    }
    
    #ifdef DebugCF // just for debugging
        Serial.println("PID Stopped");
    #endif
        //Work = 0;
        delay(20);
  }
}
