The0Scorpion/2DOF_Hover/Model/2DOF_SL/TwoDOF_ert_rtw/ert_main.c

/*
 * File: ert_main.c
 *
 * Code generated for Simulink model 'TwoDOF'.
 *
 * Model version                  : 1.6
 * Simulink Coder version         : 23.2 (R2023b) 01-Aug-2023
 * C/C++ source code generated on : Thu Jun 20 21:06:06 2024
 *
 * Target selection: ert.tlc
 * Embedded hardware selection: ARM Compatible->ARM Cortex
 * Code generation objectives: Unspecified
 * Validation result: Not run
 */

#include <stdio.h>
#include <stdlib.h>
#include "TwoDOF.h"
#include "TwoDOF_private.h"
#include "rtwtypes.h"
#include "limits.h"
#include "rt_nonfinite.h"
#include "MW_ArduinoHWInit.h"
#include "mw_freertos.h"
#define UNUSED(x)                      x = x
#define NAMELEN                        16

/* Function prototype declaration*/
void exitFcn(int sig);
void *terminateTask(void *arg);
void *baseRateTask(void *arg);
void *subrateTask(void *arg);
volatile boolean_T stopRequested = false;
volatile boolean_T runModel = true;
SemaphoreHandle_t stopSem;
SemaphoreHandle_t baserateTaskSem;
mw_thread_t schedulerThread;
mw_thread_t baseRateThread;
void *threadJoinStatus;
int terminatingmodel = 0;
void *baseRateTask(void *arg)
{
  runModel = (rtmGetErrorStatus(TwoDOF_M) == (NULL));
  while (runModel) {
    mw_osSemaphoreWaitEver(&baserateTaskSem);
    TwoDOF_step();

    /* Get model outputs here */
    stopRequested = !((rtmGetErrorStatus(TwoDOF_M) == (NULL)));
    runModel = !stopRequested;
  }

  runModel = 0;
  terminateTask(arg);
  mw_osThreadExit((void *)0);
  return NULL;
}

void exitFcn(int sig)
{
  UNUSED(sig);
  rtmSetErrorStatus(TwoDOF_M, "stopping the model");
}

void *terminateTask(void *arg)
{
  UNUSED(arg);
  terminatingmodel = 1;

  {
    runModel = 0;
  }

  /* Terminate model */
  TwoDOF_terminate();
  mw_osSemaphoreRelease(&stopSem);
  return NULL;
}

int app_main(int argc, char **argv)
{
  init();
  MW_Arduino_Init();
  rtmSetErrorStatus(TwoDOF_M, 0);

  /* Initialize model */
  TwoDOF_initialize();

  /* Call RTOS Initialization function */
  mw_RTOSInit(0.005, 0);

  /* Wait for stop semaphore */
  mw_osSemaphoreWaitEver(&stopSem);

#if (MW_NUMBER_TIMER_DRIVEN_TASKS > 0)

  {
    int i;
    for (i=0; i < MW_NUMBER_TIMER_DRIVEN_TASKS; i++) {
      CHECK_STATUS(mw_osSemaphoreDelete(&timerTaskSem[i]), 0,
                   "mw_osSemaphoreDelete");
    }
  }

#endif

  return 0;
}

/*
 * File trailer for generated code.
 *
 * [EOF]
 */
