The0Scorpion/2DOF_Hover/Codes/Processing/IDE/IDE.pde

import processing.serial.*;
Serial myPort;   
int rectX, rectY;      // Position of square button
int circleX, circleY;  // Position of circle button
int rectSize = 90;     // Diameter of rect
int circleSize = 93;   // Diameter of circle
color rectColor, circleColor, baseColor;
color rectHighlight, circleHighlight;
color currentColor;
boolean rectOver = false;
boolean circleOver = false;

void setup() {
  size(1080, 720);
  rectColor = color(0);
  rectHighlight = color(51);
  circleColor = color(255);
  circleHighlight = color(204);
  baseColor = color(102);
  currentColor = baseColor;
  circleX = width/2+circleSize/2+10;
  circleY = height/2+200;
  rectX = width/2-rectSize-10;
  rectY = height/2-rectSize/2+200;
  ellipseMode(CENTER);
  myPort = new Serial(this, Serial.list()[0], 9600);
}

void draw() {
  update(mouseX, mouseY);
  background(currentColor);
  
  if (rectOver) {
    fill(rectHighlight);
  } else {
    fill(rectColor);
  }
  stroke(255);
  rect(rectX, rectY, rectSize, rectSize);
  fill(0, 408, 612);
  textSize(10);
  text("Stop", rectX+rectSize/2-10, rectY+rectSize/2+3);   
  if (circleOver) {
    fill(circleHighlight);
  } else {
    fill(circleColor);
  }
  stroke(0);
  ellipse(circleX, circleY, circleSize, circleSize);
  fill(0, 0, 0);
  textSize(10);
  text("Start", circleX-10, circleY+3); 
}

void update(int x, int y) {
  if ( overCircle(circleX, circleY, circleSize) ) {
    circleOver = true;
    rectOver = false;
  } else if ( overRect(rectX, rectY, rectSize, rectSize) ) {
    rectOver = true;
    circleOver = false;
  } else {
    circleOver = rectOver = false;
  }
}

void mousePressed() {
  if (circleOver) {
    currentColor = circleColor;
    myPort.write('O');
  }
  if (rectOver) {
    currentColor = rectColor;
    myPort.write('S');
  }
}

boolean overRect(int x, int y, int width, int height)  {
  if (mouseX >= x && mouseX <= x+width && 
      mouseY >= y && mouseY <= y+height) {
    return true;
  } else {
    return false;
  }
}

boolean overCircle(int x, int y, int diameter) {
  float disX = x - mouseX;
  float disY = y - mouseY;
  if (sqrt(sq(disX) + sq(disY)) < diameter/2 ) {
    return true;
  } else {
    return false;
  }
}
