The0Scorpion/2DOF_Hover/Model/2DOF_SL/SourceFiles/EncoderIMU/IMU_Michael.h

/*
 * Submodule that Handles Imu functions
 * Credit:Michael 
 * Created:
 * Updated By Scorpion 
 * Last update: 4/3/2024
*/

#include "Arduino.h"
#include "Wire.h"

void updateIMU(void);
void initIMU();
float GetxPosIMU(void);
float GetyPosIMU(void);
