The0Scorpion/2DOF_Hover/Model/2DOF_SL/TwoDOF_ert_rtw/TwoDOF_types.h

/*
 * File: TwoDOF_types.h
 *
 * Code generated for Simulink model 'TwoDOF'.
 *
 * Model version                  : 1.6
 * Simulink Coder version         : 23.2 (R2023b) 01-Aug-2023
 * C/C++ source code generated on : Thu Jun 20 21:06:06 2024
 *
 * Target selection: ert.tlc
 * Embedded hardware selection: ARM Compatible->ARM Cortex
 * Code generation objectives: Unspecified
 * Validation result: Not run
 */

#ifndef RTW_HEADER_TwoDOF_types_h_
#define RTW_HEADER_TwoDOF_types_h_
#include "rtwtypes.h"
#ifndef struct_tag_svDHPqdix0CzfZjI4FSwwE
#define struct_tag_svDHPqdix0CzfZjI4FSwwE

struct tag_svDHPqdix0CzfZjI4FSwwE
{
  boolean_T matlabCodegenIsDeleted;
  int32_T isInitialized;
  boolean_T isSetupComplete;
  real_T SampleTime;
};

#endif                                 /* struct_tag_svDHPqdix0CzfZjI4FSwwE */

#ifndef typedef_Encoders_TwoDOF_T
#define typedef_Encoders_TwoDOF_T

typedef struct tag_svDHPqdix0CzfZjI4FSwwE Encoders_TwoDOF_T;

#endif                                 /* typedef_Encoders_TwoDOF_T */

#ifndef struct_tag_RDYErIHjLJEGkw9A5O4iRF
#define struct_tag_RDYErIHjLJEGkw9A5O4iRF

struct tag_RDYErIHjLJEGkw9A5O4iRF
{
  boolean_T matlabCodegenIsDeleted;
  int32_T isInitialized;
  boolean_T isSetupComplete;
  real_T SampleTime;
};

#endif                                 /* struct_tag_RDYErIHjLJEGkw9A5O4iRF */

#ifndef typedef_IMU_TwoDOF_T
#define typedef_IMU_TwoDOF_T

typedef struct tag_RDYErIHjLJEGkw9A5O4iRF IMU_TwoDOF_T;

#endif                                 /* typedef_IMU_TwoDOF_T */

#ifndef struct_tag_mZnPDIrS4QwNJro2ysYUeB
#define struct_tag_mZnPDIrS4QwNJro2ysYUeB

struct tag_mZnPDIrS4QwNJro2ysYUeB
{
  boolean_T matlabCodegenIsDeleted;
  int32_T isInitialized;
  boolean_T isSetupComplete;
  real_T SampleTime;
};

#endif                                 /* struct_tag_mZnPDIrS4QwNJro2ysYUeB */

#ifndef typedef_Motors_Propellers_TwoDOF_T
#define typedef_Motors_Propellers_TwoDOF_T

typedef struct tag_mZnPDIrS4QwNJro2ysYUeB Motors_Propellers_TwoDOF_T;

#endif                                 /* typedef_Motors_Propellers_TwoDOF_T */

/* Parameters (default storage) */
typedef struct P_TwoDOF_T_ P_TwoDOF_T;

/* Forward declaration for rtModel */
typedef struct tag_RTM_TwoDOF_T RT_MODEL_TwoDOF_T;

#endif                                 /* RTW_HEADER_TwoDOF_types_h_ */

/*
 * File trailer for generated code.
 *
 * [EOF]
 */
